hexaedron/vette/src/fsm_instructionsForABS_state.cpp

#include "ch32v003fun.h"
#include "include/cube_defs.h"

#include "include/FSM.h"

extern sh1106 OLEDScreen;
extern bool fsm_enter_state_flag;
extern void ( *fsm_state )( void );

#ifdef ECM_DEBUG
	extern A172ALDL ALDLData;
#endif

void fsm_instructionsForABS_state()
{
	// Declare local/static variable here.

	if ( fsm_enter_state_flag )
	{
		// Run once when enter this state.
		makeScreen(87, 0, 0, 32, 8);
		OLEDScreen.drawstr(8, lineNumbers[1], (char*)"Engine must be off now.", 1);
		OLEDScreen.drawstr(8, lineNumbers[3], (char*)"Press button and", 1);
		OLEDScreen.drawstr(8, lineNumbers[4], (char*)"start the engine...", 1);
		OLEDScreen.refresh();
	}

	if ( btnClick() )
	{
		makeScreen(87, 0, 0, 32, 8);
		OLEDScreen.drawstr(16, lineNumbers[2], (char*)"Initializing ABS", 1);
		OLEDScreen.drawstr(26, lineNumbers[3], (char*)"Connection...", 1);
		OLEDScreen.refresh();

		fsm_state = &fsm_drawABSErrors_state;
		fsm_enter_state_flag = true;
		return;
	}

	fsm_enter_state_flag = false; // Reset flag
}
