hexaedron/vette/include/bitmaps.h

#pragma once

// https://apps.lospec.com/pixel-editor
// https://javl.github.io/image2cpp/

const unsigned char vette_logo[] =
{  
    // 'c4-logo.gif', 88x64px
    0x00, 0x00, 0x00, 0x00, 0x01, 0xfe, 0x00, 0x00, 0x00, 0x00, 0x00, 0x00, 0x00, 0x00, 0x00, 0x7f, 
    0xff, 0xfc, 0x00, 0x00, 0x00, 0x00, 0x00, 0x00, 0x00, 0x01, 0xff, 0xff, 0xff, 0x00, 0x00, 0x00, 
    0x00, 0x00, 0x00, 0x00, 0x03, 0xff, 0xc7, 0xff, 0x80, 0x00, 0x00, 0x00, 0x00, 0x00, 0x00, 0x1f, 
    0xe0, 0x00, 0x0f, 0xf0, 0x00, 0x00, 0x00, 0x00, 0x00, 0x00, 0x3f, 0x00, 0x00, 0x01, 0xf8, 0x00, 
    0x00, 0x00, 0x00, 0x00, 0x00, 0xfc, 0x00, 0x00, 0x00, 0x7e, 0x00, 0x00, 0x00, 0x00, 0x00, 0x01, 
    0xf0, 0x00, 0x00, 0x00, 0x3f, 0x00, 0x00, 0x00, 0x00, 0x00, 0x03, 0xe0, 0x00, 0x00, 0x00, 0x0f, 
    0x80, 0x00, 0x00, 0x00, 0x00, 0x07, 0x80, 0x00, 0x00, 0x00, 0x07, 0xc0, 0x00, 0x00, 0x00, 0x00, 
    0x0f, 0x80, 0x00, 0x00, 0x00, 0x03, 0xe0, 0x00, 0x00, 0x00, 0x00, 0x1e, 0x00, 0x00, 0x00, 0x00, 
    0x00, 0xf0, 0x00, 0x00, 0x00, 0x00, 0x3c, 0x00, 0x00, 0x00, 0x00, 0x00, 0x70, 0x00, 0x00, 0x00, 
    0x00, 0x3c, 0x00, 0x00, 0x00, 0x00, 0x00, 0x78, 0x00, 0x00, 0x00, 0x00, 0x78, 0x00, 0x00, 0x00, 
    0x00, 0x00, 0x38, 0x00, 0x00, 0x00, 0x00, 0x70, 0x00, 0x00, 0x00, 0x00, 0x00, 0x1c, 0x00, 0x00, 
    0x00, 0x01, 0xf0, 0x00, 0x00, 0x00, 0x00, 0x00, 0x1e, 0x00, 0x00, 0x00, 0x01, 0xe0, 0x00, 0x00, 
    0x00, 0x00, 0x00, 0x0f, 0x00, 0x00, 0x00, 0x01, 0xc0, 0x00, 0x00, 0x00, 0x00, 0x00, 0x0f, 0x00, 
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
    0x00, 0x00, 0xfc, 0x00, 0x01, 0xfe, 0x00, 0x03, 0xff, 0xfe, 0x1f, 0xff, 0xff, 0x3f, 0xff, 0xff, 
    0x3f, 0xff, 0xff, 0x7f, 0x87, 0xfe, 0x7f, 0x03, 0xfc, 0x7e, 0x00, 0xf0, 0x7e, 0x00, 0x00, 0x7c, 
    0x00, 0x00, 0x3c, 0x00, 0x00, 0x38, 0x00, 0x00
};
