hexaedron/vette/include/line_nums.h

#pragma once

#define LINES_MAX 6

const uint8_t lineNumbers[LINES_MAX]
{
    /* line_1 = */ 12,
    /* line_2 = */ 22,
    /* line_3 = */ 32,
    /* line_4 = */ 42,
    /* line_5 = */ 52,
    /* line_6 = */ 62
};
